DoWiD-wsn/avr-based_sensor_node/source/_asnx_lib_/i2c/i2c.c

/*!
 * @brief   ASN(x) I2C (TWI) library -- source file
 *
 * Library to support the use of the I2C module.
 *
 * @file    /_asnx_lib_/i2c/i2c.c
 * @author  Dominik Widhalm
 * @version 1.2.1
 * @date    2021/12/29
 */


/***** INCLUDES *******************************************************/
#include "i2c.h"


/***** FUNCTIONS ******************************************************/
/*!
 * Initialize the I2C interface as master.
 */
void i2c_init(void) {
    /* Initialize TWI clock with no prescaler */
    TWSR = 0;
    /* TWBR should be >10 for stable operation */
    TWBR = (uint8_t)(((F_CPU/I2C_SCL_CLK)-16.0)/2.0);
}


/*!
 * Reset the I2C interface (necessary after sleep).
 */
void i2c_reset(void) {
    /* Disable TWI */
    TWCR &= ~((1 << TWSTO) | (1 << TWEN));
    /* Re-enable TWI */
    TWCR |= (1 << TWEN);
}


/*!
 * Check if a device is available at the given address.
 *
 * @param[in]   addr        The device I2C address
 * @return      OK if device is available; ERROR otherwise
 */
I2C_RET_t i2c_is_available(uint8_t addr) {
    return i2c_write_raw(addr, 0x00);
}


/*!
 * Stop I2C data transfer and release I2C bus.
 *
 * @return      OK in case of success; ERROR otherwise
 */
I2C_RET_t i2c_stop(void) {
    /* Timeout counter */
    uint8_t timeout = 0;
    /* Send STOP condition */
    TWCR = _BV(TWINT) | _BV(TWEN) | _BV(TWSTO);
    /* Wait until STOP condition is executed and bus released */
    timeout = 0;
    while(TWCR & _BV(TWSTO)){
        /* Check if timeout has been reached */
        if(timeout++ >= I2C_WAIT_TIMEOUT) {
            /* Something's wrong ... */
            return I2C_RET_ERROR;
        }
    }
    /* Return success */
    return I2C_RET_OK;
}


/*!
 * Send I2C start condition, address and transfer direction.
 *
 * @param[in]   addr        Address of I2C device
 * @param[in]   dir         Transfer direction (R/W)
 * @return      OK in case of success; ERROR otherwise
 */
I2C_RET_t i2c_start(uint8_t addr, I2C_DIR_t dir) {
    /* Variable to temporary store status register value */
    uint8_t status_tmp;
    /* Timeout counter */
    uint8_t timeout = 0;
    /* Send START condition */
    TWCR = _BV(TWINT) | _BV(TWSTA) | _BV(TWEN);
    /* Wait until transmission completed */
    timeout = 0;
    while(!(TWCR & _BV(TWINT))) {
        /* Check if timeout has been reached */
        if(timeout++ >= I2C_WAIT_TIMEOUT) {
            /* Something's wrong ... */
            return I2C_RET_ERROR;
        }
    }
    /* Check value of TWI status register */
    status_tmp = TW_STATUS;
    if((status_tmp != TW_START) && (status_tmp != TW_REP_START)) {
        /* Something's wrong ... */
        return I2C_RET_ERROR;
    }

    /* Send device address */
    TWDR = (addr<<1) | dir;
    TWCR = _BV(TWINT) | _BV(TWEN);
    /* Wail until transmission completed and ACK/NACK has been received */
    timeout = 0;
    while(!(TWCR & _BV(TWINT))) {
        /* Check if timeout has been reached */
        if(timeout++ >= I2C_WAIT_TIMEOUT) {
            /* Something's wrong ... */
            return I2C_RET_ERROR;
        }
    }
    /* Check value of TWI status register */
    status_tmp = TW_STATUS;
    if((status_tmp != TW_MT_SLA_ACK) && (status_tmp != TW_MR_SLA_ACK)) {
        /* Something's wrong ... */
        return I2C_RET_ERROR;
    }
    /* Return success */
    return I2C_RET_OK;
}


/*!
 * Send I2C repeated start condition, address and transfer direction.
 * If device is busy, use ack polling to wait until device ready.
 *
 * @param[in]   addr        Address of I2C device
 * @param[in]   dir         Transfer direction (R/W)
 * @return      OK in case of success; ERROR otherwise
 */
I2C_RET_t i2c_start_wait(uint8_t addr, I2C_DIR_t dir) {
    /* Variable to temporary store status register value */
    uint8_t status_tmp;
    /* Try counter */
    uint8_t try = 0;
    /* Timeout counter */
    uint8_t timeout = 0;
    /* Try until success or timeout reached */
    while(1) {
        /* Check if timeout has been reached */
        if(try++ >= I2C_WAIT_TIMEOUT) {
            /* Something's wrong ... */
            return I2C_RET_ERROR;
        }
        /* Send START condition */
        TWCR = _BV(TWINT) | _BV(TWSTA) | _BV(TWEN);
        /* Wait until transmission completed */
        timeout = 0;
        while(!(TWCR & _BV(TWINT))) {
            /* Check if timeout has been reached */
            if(timeout++ >= I2C_WAIT_TIMEOUT) {
                /* Something's wrong ... */
                return I2C_RET_ERROR;
            }
        }
        /* Check value of TWI status register */
        status_tmp = TW_STATUS;
        if((status_tmp != TW_START) && (status_tmp != TW_REP_START)) {
            /* Give it another try ... */
            continue;
        }
        /* Send device address */
        TWDR = (addr<<1) | dir;
        TWCR = _BV(TWINT) | _BV(TWEN);
        /* Wail until transmission completed */
        timeout = 0;
        while(!(TWCR & _BV(TWINT))) {
            /* Check if timeout has been reached */
            if(timeout++ >= I2C_WAIT_TIMEOUT) {
                /* Something's wrong ... */
                return I2C_RET_ERROR;
            }
        }
        /* Check value of TWI status register */
        status_tmp = TW_STATUS;
        if((status_tmp == TW_MT_SLA_NACK) || (status_tmp ==TW_MR_DATA_NACK)) {
            /* Device busy, send stop condition to terminate write operation */
            i2c_stop();
            /* Give it another try ... */
            continue;
        }
        /* Looks like we've gone through ... */
        break;
    }
    /* Return success */
    return I2C_RET_OK;
}


/*!
 * Write one byte to I2C device.
 *
 * @param[in]   data        Data byte to be transferred
 * @return      OK in case of success; ERROR otherwise
 */
I2C_RET_t i2c_put(uint8_t data) {
    /* Timeout counter */
    uint8_t timeout = 0;
    /* Variable to temporary store status register value */
    uint8_t status_tmp;
    /* Send data to the previously addressed device */
    TWDR = data;
    TWCR = _BV(TWINT) | _BV(TWEN);
    /* Wait until transmission completed */
    timeout = 0;
    while(!(TWCR & _BV(TWINT))) {
        /* Check if timeout has been reached */
        if(timeout++ >= I2C_WAIT_TIMEOUT) {
            /* Something's wrong ... */
            return I2C_RET_ERROR;
        }
    }
    /* Check value of TWI status register */
    status_tmp = TW_STATUS;
    if(status_tmp != TW_MT_DATA_ACK) {
        /* Something's wrong ... */
        return I2C_RET_ERROR;
    }
    /* Return success */
    return I2C_RET_OK;
}


/*!
 * Read one byte from the I2C device with ACK (request more data from device).
 *
 * @param[out]  data        Data byte memory location
 * @return      OK in case of success; ERROR otherwise
 */
I2C_RET_t i2c_get_ack(uint8_t* data) {
    /* Timeout counter */
    uint8_t timeout = 0;
    /* Send a read request with acknowledgement (ack) */
    TWCR = _BV(TWINT) | _BV(TWEN) | _BV(TWEA);
    /* Wait until read is complete */
    timeout = 0;
    while(!(TWCR & _BV(TWINT))) {
        /* Check if timeout has been reached */
        if(timeout++ >= I2C_WAIT_TIMEOUT) {
            /* Something's wrong ... */
            return I2C_RET_ERROR;
        }
    }
    /* Copy the received byte */
    *data = TWDR;
    /* Return success */
    return I2C_RET_OK;
}


/*!
 * Read one byte from the I2C device with NACK (read is followed by a stop condition).
 *
 * @param[out]  data        Data byte memory location
 * @return      OK in case of success; ERROR otherwise
 */
I2C_RET_t i2c_get_nack(uint8_t* data) {
    /* Timeout counter */
    uint8_t timeout = 0;
    /* Send a read request without acknowledgement (nack) */
    TWCR = _BV(TWINT) | _BV(TWEN);
    /* Wait until read is complete */
    timeout = 0;
    while(!(TWCR & _BV(TWINT))) {
        /* Check if timeout has been reached */
        if(timeout++ >= I2C_WAIT_TIMEOUT) {
            /* Something's wrong ... */
            return I2C_RET_ERROR;
        }
    }
    /* Copy the received byte */
    *data = TWDR;
    /* Return success */
    return I2C_RET_OK;
}


/*!
 * Write 8-bit data to a given I2C address.
 *
 * @param[in]   addr        Address of I2C device
 * @param[in]   value       Data byte to be written
 * @return      OK in case of success; ERROR otherwise
 */
I2C_RET_t i2c_write_raw(uint8_t addr, uint8_t value) {
    /* Start in writing mode */
    if(i2c_start_wait(addr, I2C_WRITE) != I2C_RET_OK) {
        /* Start failed */
        return I2C_RET_ERROR;
    }
    /* Write value byte */
    if(i2c_put(value) != I2C_RET_OK) {
        /* Write byte failed */
        return I2C_RET_ERROR;
    }
    /* Stop writing mode */
    if(i2c_stop() != I2C_RET_OK) {
        /* Stop failed */
        return I2C_RET_ERROR;
    }
    /* Return with success */
    return I2C_RET_OK;
}


/*!
 * Read 8-bit data from a given I2C address.
 *
 * @param[in]   addr        Address of I2C device
 * @param[out]  value       Data byte memory location
 * @return      OK in case of success; ERROR otherwise
 */
I2C_RET_t i2c_read_raw(uint8_t addr, uint8_t* value) {
    /* Start in reading mode */
    if(i2c_start_wait(addr, I2C_READ) != I2C_RET_OK) {
        /* Start failed */
        return I2C_RET_ERROR;
    }
    /* Read a byte */
    uint8_t tmp;
    /* Read with NACK */
    if(i2c_get_nack(&tmp) == I2C_RET_OK) {
        /* Copy read byte */
        *value = tmp;
    } else {
        /* Read failed */
        return I2C_RET_ERROR;
    }
    /* Stop reading mode */
    if(i2c_stop() != I2C_RET_OK) {
        /* Stop failed */
        return I2C_RET_ERROR;
    }
    /* Return with success */
    return I2C_RET_OK;
}


/*!
 * Write a defined number of data bytes to a register of a given I2C address.
 *
 * @param[in]   addr        Address of I2C device
 * @param[in]   reg         Device register address
 * @param[in]   value       Data bytes to be written
 * @param[in]   len         Number of bytes to be written
 * @return      OK in case of success; ERROR otherwise
 */
I2C_RET_t i2c_write_block(uint8_t addr, uint8_t reg, uint8_t* value, uint8_t len) {
    /* Start in writing mode */
    if(i2c_start_wait(addr, I2C_WRITE) != I2C_RET_OK) {
        /* Start failed */
        return I2C_RET_ERROR;
    }
    /* Write register address */
    if(i2c_put(reg) != I2C_RET_OK) {
        /* Write address failed */
        return I2C_RET_ERROR;
    }
    /* Write "len" bytes */
    uint8_t cnt;
    for(cnt=0; cnt<len; cnt++) {
        /* Write cnt. byte */
        if(i2c_put(value[cnt]) != I2C_RET_OK) {
            /* Write byte failed */
            return I2C_RET_ERROR;
        }
    }
    /* Stop writing mode */
    if(i2c_stop() != I2C_RET_OK) {
        /* Stop failed */
        return I2C_RET_ERROR;
    }
    /* Return with success */
    return I2C_RET_OK;
}


/*!
 * Write 8-bit data to a register of a given I2C address.
 *
 * @param[in]   addr        Address of I2C device
 * @param[in]   reg         Device register address
 * @param[in]   value       8-bit data to be written
 * @return      OK in case of success; ERROR otherwise
 */
I2C_RET_t i2c_write_8(uint8_t addr, uint8_t reg, uint8_t value) {
    /* Start in writing mode */
    if(i2c_start_wait(addr, I2C_WRITE) != I2C_RET_OK) {
        /* Start failed */
        return I2C_RET_ERROR;
    }
    /* Write register address */
    if(i2c_put(reg) != I2C_RET_OK) {
        /* Write address failed */
        return I2C_RET_ERROR;
    }
    /* Write value byte */
    if(i2c_put(value) != I2C_RET_OK) {
        /* Write byte failed */
        return I2C_RET_ERROR;
    }
    /* Stop writing mode */
    if(i2c_stop() != I2C_RET_OK) {
        /* Stop failed */
        return I2C_RET_ERROR;
    }
    /* Return with success */
    return I2C_RET_OK;
}


/*!
 * Write 16-bit data to a register of a given I2C address.
 *
 * @param[in]   addr        Address of I2C device
 * @param[in]   reg         Device register address
 * @param[in]   value       16-bit data to be written
 * @return      OK in case of success; ERROR otherwise
 */
I2C_RET_t i2c_write_16(uint8_t addr, uint8_t reg, uint16_t value) {
    /* Start in writing mode */
    if(i2c_start_wait(addr, I2C_WRITE) != I2C_RET_OK) {
        /* Start failed */
        return I2C_RET_ERROR;
    }
    /* Write register address */
    if(i2c_put(reg) != I2C_RET_OK) {
        /* Write address failed */
        return I2C_RET_ERROR;
    }
    /* Write value lower byte */
    if(i2c_put(value & 0x00FF) != I2C_RET_OK) {
        /* Write byte failed */
        return I2C_RET_ERROR;
    }
    /* Write value higher byte */
    if(i2c_put((value & 0xFF00) >> 8) != I2C_RET_OK) {
        /* Write byte failed */
        return I2C_RET_ERROR;
    }
    /* Stop writing mode */
    if(i2c_stop() != I2C_RET_OK) {
        /* Stop failed */
        return I2C_RET_ERROR;
    }
    /* Return with success */
    return I2C_RET_OK;
}


/*!
 * Read a defined number of data bytes from a register of a given I2C address.
 *
 * @param[in]   addr        Address of I2C device
 * @param[in]   reg         Device register address
 * @param[out]  value       Data bytes memory location
 * @param[in]   len         Number of bytes to be read
 * @return      OK in case of success; ERROR otherwise
 */
I2C_RET_t i2c_read_block(uint8_t addr, uint8_t reg, uint8_t* value, uint8_t len) {
    /* Start in writing mode */
    if(i2c_start_wait(addr, I2C_WRITE) != I2C_RET_OK) {
        /* Start failed */
        return I2C_RET_ERROR;
    }
    /* Write register address */
    if(i2c_put(reg) != I2C_RET_OK) {
        /* Write address failed */
        return I2C_RET_ERROR;
    }
    /* Stop writing mode */
    if(i2c_stop() != I2C_RET_OK) {
        /* Write byte failed */
        return I2C_RET_ERROR;
    }
    
    /* Restart in reading mode */
    if(i2c_start_wait(addr, I2C_READ) != I2C_RET_OK) {
        /* Start failed */
        return I2C_RET_ERROR;
    }
    /* Read "len" bytes */
    uint8_t cnt,tmp;
    for(cnt=0; cnt<len; cnt++) {
        /* Check whether it is the last byte to read */
        if(cnt<(len-1)) {
            /* Read with ACK */
            if(i2c_get_ack(&tmp) == I2C_RET_OK) {
                /* Copy read byte */
                value[cnt] = tmp;
            } else {
                /* Read failed */
                return I2C_RET_ERROR;
            }
        } else {
            /* Read with NACK */
            if(i2c_get_nack(&tmp) == I2C_RET_OK) {
                /* Copy read byte */
                value[cnt] = tmp;
            } else {
                /* Read failed */
                return I2C_RET_ERROR;
            }
        }
    }
    /* Stop reading mode */
    if(i2c_stop() != I2C_RET_OK) {
        /* Stop failed */
        return I2C_RET_ERROR;
    }
    /* Return with success */
    return I2C_RET_OK;
}


/*!
 * Read 8-bit data (unsigned) from a register of a given I2C address.
 *
 * @param[in]   addr        Address of I2C device
 * @param[in]   reg         Device register address
 * @param[out]  value       8-bit data memory location
 * @return      OK in case of success; ERROR otherwise
 */
I2C_RET_t i2c_read_U8(uint8_t addr, uint8_t reg, uint8_t* value) {
/* Start in writing mode */
    if(i2c_start_wait(addr, I2C_WRITE) != I2C_RET_OK) {
        /* Start failed */
        return I2C_RET_ERROR;
    }
    /* Write register address */
    if(i2c_put(reg) != I2C_RET_OK) {
        /* Write address failed */
        return I2C_RET_ERROR;
    }
    /* Stop writing mode */
    if(i2c_stop() != I2C_RET_OK) {
        /* Write byte failed */
        return I2C_RET_ERROR;
    }
    
    /* Restart in reading mode */
    if(i2c_start_wait(addr, I2C_READ) != I2C_RET_OK) {
        /* Start failed */
        return I2C_RET_ERROR;
    }
    /* Read 8 bit */
    uint8_t tmp;
    /* Read with NACK */
    if(i2c_get_nack(&tmp) == I2C_RET_OK) {
        /* Copy read byte */
        *value = tmp;
    } else {
        /* Read failed */
        return I2C_RET_ERROR;
    }
    /* Stop reading mode */
    if(i2c_stop() != I2C_RET_OK) {
        /* Stop failed */
        return I2C_RET_ERROR;
    }
    /* Return with success */
    return I2C_RET_OK;
}


/*!
 * Read signed 8-bit data from a register of a given I2C address.
 *
 * @param[in]   addr        Address of I2C device
 * @param[in]   reg         Device register address
 * @param[out]  value       Signed 8-bit data memory location
 * @return      OK in case of success; ERROR otherwise
 */
I2C_RET_t i2c_read_S8(uint8_t addr, uint8_t reg, int8_t* value) {
    uint8_t tmp;
    /* Read 8-bit unsigned */
    if(i2c_read_U8(addr, reg, &tmp) != I2C_RET_OK) {
        /* Read failed */
        return I2C_RET_ERROR;
    }
    /* Check if tmp sign bit is set */
    if(tmp > 127) {
        /* Negative value */
        *value = tmp-256;
    } else {
        /* Positive value */
        *value = tmp;
    }
    /* Return with success */
    return I2C_RET_OK;
}


/*!
 * Read 16-bit data (unsigned) with a given endianess from a register of a given I2C address.
 *
 * @param[in]   addr        Address of I2C device
 * @param[in]   reg         Device register address
 * @param[out]  value       16-bit data memory location
 * @param[in]   endian      Endianess of the data bytes
 * @return      OK in case of success; ERROR otherwise
 */
I2C_RET_t i2c_read_U16(uint8_t addr, uint8_t reg, uint16_t* value, I2C_ENDIAN_t endian) {
    uint8_t tmp[2];
    /* Read two byte */
    if(i2c_read_block(addr, reg, tmp, 2) != I2C_RET_OK) {
        /* Read failed */
        return I2C_RET_ERROR;
    }
    /* Swap bytes if using big endian */
    if(endian == I2C_ENDIAN_BIG) {
        /* Big Endian */
        *value = ((uint16_t)tmp[0]<<8) | (uint16_t)tmp[1];
    } else {
        /* Little Endian */
        *value = ((uint16_t)tmp[1]<<8) | (uint16_t)tmp[0];
    }
    /* Return with success */
    return I2C_RET_OK;
}


/*!
 * Read signed 16-bit data with a given endianess from a register of a given I2C address.
 *
 * @param[in]   addr        Address of I2C device
 * @param[in]   reg         Device register address
 * @param[out]  value       Signed 16-bit data memory location
 * @param[in]   endian      Endianess of the data bytes
 * @return      OK in case of success; ERROR otherwise
 */
I2C_RET_t i2c_read_S16(uint8_t addr, uint8_t reg, int16_t* value, I2C_ENDIAN_t endian) {
    uint16_t tmp;
    /* Read 16-bit unsigned */
    if(i2c_read_U16(addr, reg, &tmp, endian) != I2C_RET_OK) {
        /* Read failed */
        return I2C_RET_ERROR;
    }
    /* Check if tmp sign bit is set */
    if(tmp > 32767) {
        /* Negative value */
        *value = tmp-65536;
    } else {
        /* Positive value */
        *value = tmp;
    }
    /* Return with success */
    return I2C_RET_OK;
}


/*!
 * Read 16-bit little endian data (unsigned) from a register of a given I2C address.
 *
 * @param[in]   addr        Address of I2C device
 * @param[in]   reg         Device register address
 * @param[out]  value       16-bit LE data memory location
 * @return      OK in case of success; ERROR otherwise
 */
I2C_RET_t i2c_read_U16LE(uint8_t addr, uint8_t reg, uint16_t* value) {
    uint16_t tmp;
    /* Read 16-bit unsigned */
    if(i2c_read_U16(addr, reg, &tmp, I2C_ENDIAN_LITTLE) != I2C_RET_OK) {
        /* Read failed */
        return I2C_RET_ERROR;
    }
    /* Copy value */
    *value = tmp;
    /* Return with success */
    return I2C_RET_OK;
}


/*!
 * Read 16-bit big endian data (unsigned) from a register of a given I2C address.
 *
 * @param[in]   addr        Address of I2C device
 * @param[in]   reg         Device register address
 * @param[out]  value       16-bit BE data memory location
 * @return      OK in case of success; ERROR otherwise
 */
I2C_RET_t i2c_read_U16BE(uint8_t addr, uint8_t reg, uint16_t* value) {
    uint16_t tmp;
    /* Read 16-bit unsigned */
    if(i2c_read_U16(addr, reg, &tmp, I2C_ENDIAN_BIG) != I2C_RET_OK) {
        /* Read failed */
        return I2C_RET_ERROR;
    }
    /* Copy value */
    *value = tmp;
    /* Return with success */
    return I2C_RET_OK;
}


/*!
 * Read signed 16-bit little endian data from a register of a given I2C address.
 *
 * @param[in]   addr        Address of I2C device
 * @param[in]   reg         Device register address
 * @param[out]  value       Signed 16-bit LE data memory location
 * @return      OK in case of success; ERROR otherwise
 */
I2C_RET_t i2c_read_S16LE(uint8_t addr, uint8_t reg, int16_t* value) {
    int16_t tmp;
    /* Read 16-bit signed */
    if(i2c_read_S16(addr, reg, &tmp, I2C_ENDIAN_LITTLE) != I2C_RET_OK) {
        /* Read failed */
        return I2C_RET_ERROR;
    }
    /* Copy value */
    *value = tmp;
    /* Return with success */
    return I2C_RET_OK;
}


/*!
 * Read signed 16-bit big endian data from a register of a given I2C address.
 *
 * @param[in]   addr        Address of I2C device
 * @param[in]   reg         Device register address
 * @param[out]  value       Signed 16-bit BE data memory location
 * @return      OK in case of success; ERROR otherwise
 */
I2C_RET_t i2c_read_S16BE(uint8_t addr, uint8_t reg, int16_t* value) {
    int16_t tmp;
    /* Read 16-bit signed */
    if(i2c_read_S16(addr, reg, &tmp, I2C_ENDIAN_BIG) != I2C_RET_OK) {
        /* Read failed */
        return I2C_RET_ERROR;
    }
    /* Copy value */
    *value = tmp;
    /* Return with success */
    return I2C_RET_OK;
}


/*!
 * Write a defined number of data bytes to a 16-bit register address of a given I2C address.
 *
 * @param[in]   addr        Address of I2C device
 * @param[in]   reg         16-bit device register address
 * @param[in]   value       Data bytes to be written
 * @param[in]   len         Number of bytes to be written
 * @return      OK in case of success; ERROR otherwise
 */
I2C_RET_t i2c_write16_block(uint8_t addr, uint16_t reg, uint8_t* value, uint8_t len) {
    /* Start in writing mode */
    if(i2c_start_wait(addr, I2C_WRITE) != I2C_RET_OK) {
        /* Start failed */
        return I2C_RET_ERROR;
    }
    /* Write register address low byte */
    if(i2c_put(reg & 0x00FF) != I2C_RET_OK) {
        /* Write address failed */
        return I2C_RET_ERROR;
    }
    /* Write register address high byte */
    if(i2c_put((reg & 0xFF00)>>8) != I2C_RET_OK) {
        /* Write address failed */
        return I2C_RET_ERROR;
    }
    /* Write "len" bytes */
    uint8_t cnt;
    for(cnt=0; cnt<len; cnt++) {
        /* Write cnt. byte */
        if(i2c_put(value[cnt]) != I2C_RET_OK) {
            /* Write byte failed */
            return I2C_RET_ERROR;
        }
    }
    /* Stop writing mode */
    if(i2c_stop() != I2C_RET_OK) {
        /* Stop failed */
        return I2C_RET_ERROR;
    }
    /* Return with success */
    return I2C_RET_OK;
}


/*!
 * Write 8-bit data to a 16-bit register address of a given I2C address.
 *
 * @param[in]   addr        Address of I2C device
 * @param[in]   reg         16-bit device register address
 * @param[in]   value       8-bit data to be written
 * @return      OK in case of success; ERROR otherwise
 */
I2C_RET_t i2c_write16_8(uint8_t addr, uint16_t reg, uint8_t value) {
    /* Start in writing mode */
    if(i2c_start_wait(addr, I2C_WRITE) != I2C_RET_OK) {
        /* Start failed */
        return I2C_RET_ERROR;
    }
    /* Write register address low byte */
    if(i2c_put(reg & 0x00FF) != I2C_RET_OK) {
        /* Write address failed */
        return I2C_RET_ERROR;
    }
    /* Write register address high byte */
    if(i2c_put((reg & 0xFF00)>>8) != I2C_RET_OK) {
        /* Write address failed */
        return I2C_RET_ERROR;
    }
    /* Write value byte */
    if(i2c_put(value) != I2C_RET_OK) {
        /* Write byte failed */
        return I2C_RET_ERROR;
    }
    /* Stop writing mode */
    if(i2c_stop() != I2C_RET_OK) {
        /* Stop failed */
        return I2C_RET_ERROR;
    }
    /* Return with success */
    return I2C_RET_OK;
}


/*!
 * Write 16-bit data to a 16-bit register address of a given I2C address.
 *
 * @param[in]   addr        Address of I2C device
 * @param[in]   reg         16-bit device register address
 * @param[in]   value       16-bit data to be written
 * @return      OK in case of success; ERROR otherwise
 */
I2C_RET_t i2c_write16_16(uint8_t addr, uint16_t reg, uint16_t value) {
    /* Start in writing mode */
    if(i2c_start_wait(addr, I2C_WRITE) != I2C_RET_OK) {
        /* Start failed */
        return I2C_RET_ERROR;
    }
    /* Write register address low byte */
    if(i2c_put(reg & 0x00FF) != I2C_RET_OK) {
        /* Write address failed */
        return I2C_RET_ERROR;
    }
    /* Write register address high byte */
    if(i2c_put((reg & 0xFF00)>>8) != I2C_RET_OK) {
        /* Write address failed */
        return I2C_RET_ERROR;
    }
    /* Write value lower byte */
    if(i2c_put(value & 0x00FF) != I2C_RET_OK) {
        /* Write byte failed */
        return I2C_RET_ERROR;
    }
    /* Write value higher byte */
    if(i2c_put((value & 0xFF00) >> 8) != I2C_RET_OK) {
        /* Write byte failed */
        return I2C_RET_ERROR;
    }
    /* Stop writing mode */
    if(i2c_stop() != I2C_RET_OK) {
        /* Stop failed */
        return I2C_RET_ERROR;
    }
    /* Return with success */
    return I2C_RET_OK;
}


/*!
 * Read a defined number of data bytes from a 16-bit register address of a given I2C address.
 *
 * @param[in]   addr        Address of I2C device
 * @param[in]   reg         16-bit device register address
 * @param[out]  value       Data bytes memory location
 * @param[in]   len         Number of bytes to be read
 * @return      OK in case of success; ERROR otherwise
 */
I2C_RET_t i2c_read16_block(uint8_t addr, uint16_t reg, uint8_t* value, uint8_t len) {
    /* Start in writing mode */
    if(i2c_start_wait(addr, I2C_WRITE) != I2C_RET_OK) {
        /* Start failed */
        return I2C_RET_ERROR;
    }
    /* Write register address low byte */
    if(i2c_put(reg & 0x00FF) != I2C_RET_OK) {
        /* Write address failed */
        return I2C_RET_ERROR;
    }
    /* Write register address high byte */
    if(i2c_put((reg & 0xFF00)>>8) != I2C_RET_OK) {
        /* Write address failed */
        return I2C_RET_ERROR;
    }
    /* Stop writing mode */
    if(i2c_stop() != I2C_RET_OK) {
        /* Write byte failed */
        return I2C_RET_ERROR;
    }
    
    /* Restart in reading mode */
    if(i2c_start_wait(addr, I2C_READ) != I2C_RET_OK) {
        /* Start failed */
        return I2C_RET_ERROR;
    }
    /* Read "len" bytes */
    uint8_t cnt,tmp;
    for(cnt=0; cnt<len; cnt++) {
        /* Check whether it is the last byte to read */
        if(cnt<(len-1)) {
            /* Read with ACK */
            if(i2c_get_ack(&tmp) == I2C_RET_OK) {
                /* Copy read byte */
                value[cnt] = tmp;
            } else {
                /* Read failed */
                return I2C_RET_ERROR;
            }
        } else {
            /* Read with NACK */
            if(i2c_get_nack(&tmp) == I2C_RET_OK) {
                /* Copy read byte */
                value[cnt] = tmp;
            } else {
                /* Read failed */
                return I2C_RET_ERROR;
            }
        }
    }
    /* Stop reading mode */
    if(i2c_stop() != I2C_RET_OK) {
        /* Stop failed */
        return I2C_RET_ERROR;
    }
    /* Return with success */
    return I2C_RET_OK;
}


/*!
 * Read 8-bit data (unsigned) from a 16-bit register address of a given I2C address.
 *
 * @param[in]   addr        Address of I2C device
 * @param[in]   reg         16-bit device register address
 * @param[out]  value       8-bit data memory location
 * @return      OK in case of success; ERROR otherwise
 */
I2C_RET_t i2c_read16_U8(uint8_t addr, uint16_t reg, uint8_t* value) {
/* Start in writing mode */
    if(i2c_start_wait(addr, I2C_WRITE) != I2C_RET_OK) {
        /* Start failed */
        return I2C_RET_ERROR;
    }
    /* Write register address low byte */
    if(i2c_put(reg & 0x00FF) != I2C_RET_OK) {
        /* Write address failed */
        return I2C_RET_ERROR;
    }
    /* Write register address high byte */
    if(i2c_put((reg & 0xFF00)>>8) != I2C_RET_OK) {
        /* Write address failed */
        return I2C_RET_ERROR;
    }
    /* Stop writing mode */
    if(i2c_stop() != I2C_RET_OK) {
        /* Write byte failed */
        return I2C_RET_ERROR;
    }
    
    /* Restart in reading mode */
    if(i2c_start_wait(addr, I2C_READ) != I2C_RET_OK) {
        /* Start failed */
        return I2C_RET_ERROR;
    }
    /* Read 8 bit */
    uint8_t tmp;
    /* Read with NACK */
    if(i2c_get_nack(&tmp) == I2C_RET_OK) {
        /* Copy read byte */
        *value = tmp;
    } else {
        /* Read failed */
        return I2C_RET_ERROR;
    }
    /* Stop reading mode */
    if(i2c_stop() != I2C_RET_OK) {
        /* Stop failed */
        return I2C_RET_ERROR;
    }
    /* Return with success */
    return I2C_RET_OK;
}


/*!
 * Read signed 8-bit data from a 16-bit register address of a given I2C address.
 *
 * @param[in]   addr        Address of I2C device
 * @param[in]   reg         16-bit device register address
 * @param[out]  value       Signed 8-bit data memory location
 * @return      OK in case of success; ERROR otherwise
 */
I2C_RET_t i2c_read16_S8(uint8_t addr, uint16_t reg, int8_t* value) {
    uint8_t tmp;
    /* Read 8-bit unsigned */
    if(i2c_read16_U8(addr, reg, &tmp) != I2C_RET_OK) {
        /* Read failed */
        return I2C_RET_ERROR;
    }
    /* Check if tmp sign bit is set */
    if(tmp > 127) {
        /* Negative value */
        *value = tmp-256;
    } else {
        /* Positive value */
        *value = tmp;
    }
    /* Return with success */
    return I2C_RET_OK;
}


/*!
 * Read 16-bit data (unsigned) with a given endianess from a 16-bit register address of a given I2C address.
 *
 * @param[in]   addr        Address of I2C device
 * @param[in]   reg         16-bit device register address
 * @param[out]  value       16-bit data memory location
 * @param[in]   endian      Endianess of the data bytes
 * @return      OK in case of success; ERROR otherwise
 */
I2C_RET_t i2c_read16_U16(uint8_t addr, uint16_t reg, uint16_t* value, I2C_ENDIAN_t endian) {
    uint8_t tmp[2];
    /* Read two byte */
    if(i2c_read16_block(addr, reg, tmp, 2) != I2C_RET_OK) {
        /* Read failed */
        return I2C_RET_ERROR;
    }
    /* Swap bytes if using big endian */
    if(endian == I2C_ENDIAN_BIG) {
        /* Big Endian */
        *value = ((uint16_t)tmp[0]<<8) | (uint16_t)tmp[1];
    } else {
        /* Little Endian */
        *value = ((uint16_t)tmp[1]<<8) | (uint16_t)tmp[0];
    }
    /* Return with success */
    return I2C_RET_OK;
}


/*!
 * Read signed 16-bit data with a given endianess from a 16-bit register address of a given I2C address.
 *
 * @param[in]   addr        Address of I2C device
 * @param[in]   reg         16-bit device register address
 * @param[out]  value       Signed 16-bit data memory location
 * @param[in]   endian      Endianess of the data bytes
 * @return      OK in case of success; ERROR otherwise
 */
I2C_RET_t i2c_read16_S16(uint8_t addr, uint16_t reg, int16_t* value, I2C_ENDIAN_t endian) {
    uint16_t tmp;
    /* Read 16-bit unsigned */
    if(i2c_read16_U16(addr, reg, &tmp, endian) != I2C_RET_OK) {
        /* Read failed */
        return I2C_RET_ERROR;
    }
    /* Check if tmp sign bit is set */
    if(tmp > 32767) {
        /* Negative value */
        *value = tmp-65536;
    } else {
        /* Positive value */
        *value = tmp;
    }
    /* Return with success */
    return I2C_RET_OK;
}


/*!
 * Read 16-bit little endian data (unsigned) from a 16-bit register address of a given I2C address.
 *
 * @param[in]   addr        Address of I2C device
 * @param[in]   reg         16-bit device register address
 * @param[out]  value       16-bit LE data memory location
 * @return      OK in case of success; ERROR otherwise
 */
I2C_RET_t i2c_read16_U16LE(uint8_t addr, uint16_t reg, uint16_t* value) {
    uint16_t tmp;
    /* Read 16-bit unsigned */
    if(i2c_read16_U16(addr, reg, &tmp, I2C_ENDIAN_LITTLE) != I2C_RET_OK) {
        /* Read failed */
        return I2C_RET_ERROR;
    }
    /* Copy value */
    *value = tmp;
    /* Return with success */
    return I2C_RET_OK;
}


/*!
 * Read 16-bit big endian data (unsigned) from a 16-bit register address of a given I2C address.
 *
 * @param[in]   addr        Address of I2C device
 * @param[in]   reg         16-bit device register address
 * @param[out]  value       16-bit BE data memory location
 * @return      OK in case of success; ERROR otherwise
 */
I2C_RET_t i2c_read16_U16BE(uint8_t addr, uint16_t reg, uint16_t* value) {
    uint16_t tmp;
    /* Read 16-bit unsigned */
    if(i2c_read16_U16(addr, reg, &tmp, I2C_ENDIAN_BIG) != I2C_RET_OK) {
        /* Read failed */
        return I2C_RET_ERROR;
    }
    /* Copy value */
    *value = tmp;
    /* Return with success */
    return I2C_RET_OK;
}


/*!
 * Read signed 16-bit little endian data from a 16-bit register address of a given I2C address.
 *
 * @param[in]   addr        Address of I2C device
 * @param[in]   reg         16-bit device register address
 * @param[out]  value       Signed 16-bit LE data memory location
 * @return      OK in case of success; ERROR otherwise
 */
I2C_RET_t i2c_read16_S16LE(uint8_t addr, uint16_t reg, int16_t* value) {
    int16_t tmp;
    /* Read 16-bit signed */
    if(i2c_read16_S16(addr, reg, &tmp, I2C_ENDIAN_LITTLE) != I2C_RET_OK) {
        /* Read failed */
        return I2C_RET_ERROR;
    }
    /* Copy value */
    *value = tmp;
    /* Return with success */
    return I2C_RET_OK;
}


/*!
 * Read signed 16-bit big endian data from a 16-bit register address of a given I2C address.
 *
 * @param[in]   addr        Address of I2C device
 * @param[in]   reg         16-bit device register address
 * @param[out]  value       Signed 16-bit BE data memory location
 * @return      OK in case of success; ERROR otherwise
 */
I2C_RET_t i2c_read16_S16BE(uint8_t addr, uint16_t reg, int16_t* value) {
    int16_t tmp;
    /* Read 16-bit signed */
    if(i2c_read16_S16(addr, reg, &tmp, I2C_ENDIAN_BIG) != I2C_RET_OK) {
        /* Read failed */
        return I2C_RET_ERROR;
    }
    /* Copy value */
    *value = tmp;
    /* Return with success */
    return I2C_RET_OK;
}
