DoWiD-wsn/avr-based_sensor_node/source/_asnx_lib_/sensors/stemma_soil.c

/*!
 * @brief   ASN(x) STEMMA SOIL sensor library -- source file
 *
 * Library to support the STEMMA SOIL sensor.
 *
 * @file    /_asnx_lib_/sensors/stemma_soil.c
 * @author  Dominik Widhalm
 * @version 1.2.0
 * @date    2021/06/07
 *
 * @see     https://learn.adafruit.com/adafruit-stemma-soil-sensor-i2c-capacitive-moisture-sensor/
 * @see     https://github.com/adafruit/Adafruit_Seesaw
 */


/***** INCLUDES *******************************************************/
#include "stemma_soil.h"


/***** FUNCTIONS ******************************************************/
/*!
 * Initialization of the STEMMA SOIL sensor.
 *
 * @param[out]  dev             Device structure to be filled
 * @param[in]   address         I2C address of the sensor
 */
STEMMA_RET_t stemma_init(STEMMA_t* dev, uint8_t address) {
   /* Check if the device is available */
   if(i2c_is_available(address) == I2C_RET_OK) {
        /* Device is available ... store address in device structure */
        dev->address = address;
        /* Return OK */
        return STEMMA_RET_OK;
   } else {
        /* Return ERROR */
        return STEMMA_RET_ERROR_NODEV;
   }
}


/*!
 * Read the version code of the STEMMA SOIL sensor.
 * Bits [31:16] will be a date code, [15:0] will be the product id.
 * 
 * @param[in]   dev             Device structure
 * @param[out]  version         Version code read from the sensor
 * @return      OK in case of success; ERROR otherwise
 */
STEMMA_RET_t stemma_get_version(STEMMA_t* dev, uint32_t* version) {
    /* Variable for the read result */
    uint8_t res[4] = {0};
    /* Read in 4 bytes */
    if(i2c_read16_block(dev->address, (STEMMA_STATUS_BASE | (STEMMA_STATUS_VERSION<<8)), res, 4) != I2C_RET_OK) {
        /* Reading failed */
        return STEMMA_RET_ERROR;
    }
    /* Copy the result */
    *version = ((uint32_t)res[0] << 24) | ((uint32_t)res[1] << 16) | ((uint32_t)res[2] << 8) | (uint32_t)res[3];
    /* Return success */
    return STEMMA_RET_OK;
}


/*!
 * Read the temperature of the sensor in degrees Celsius (°C).
 * 
 * @param[in]   dev             Device structure
 * @param[out]  temperature     Sensor temperature in degrees Celsius (°C)
 * @return      OK in case of success; ERROR otherwise
 */
STEMMA_RET_t stemma_get_temperature(STEMMA_t* dev, float* temperature) {
    /* Variable for the read result */
    uint8_t res[4] = {0};
    /* Read in 4 bytes */
    if(i2c_read16_block(dev->address, (STEMMA_STATUS_BASE | (STEMMA_STATUS_TEMP<<8)), res, 4) != I2C_RET_OK) {
        /* Reading failed */
        return STEMMA_RET_ERROR;
    }
    /* Get intermediate result */
    uint32_t ret = ((uint32_t)res[0] << 24) | ((uint32_t)res[1] << 16) | ((uint32_t)res[2] << 8) | (uint32_t)res[3];
    /* Copy the result */
    *temperature = (1.0 / (1UL << 16)) * (float)ret;
    /* Return success */
    return STEMMA_RET_OK;
}


/*!
 * Read the humidity of the sensor indicated by its capacitance.
 * 
 * @param[in]   dev             Device structure
 * @param[out]  humidity        Humidity in percent
 * @return      OK in case of success; ERROR otherwise
 */
STEMMA_RET_t stemma_get_humidity(STEMMA_t* dev, float* humidity) {
    /* Variable for the read result */
    uint16_t ret = STEMMA_TOUCH_WORKING;
    /* Capacitance measurement can take some time */
    do {
        /* Read in 2 bytes */
        if(i2c_read16_U16BE(dev->address, (STEMMA_TOUCH_BASE | (STEMMA_TOUCH_CH0<<8)), &ret) != I2C_RET_OK) {
            /* Reading failed */
            return STEMMA_RET_ERROR;
        }
    }while(ret == STEMMA_TOUCH_WORKING);
    /* Copy the result */
    *humidity = (((float)ret - STEMMA_CAP_MIN) / (STEMMA_CAP_MAX - STEMMA_CAP_MIN)) * 100.0;
    /* Return success */
    return STEMMA_RET_OK;
}


/*!
 * Read the humidity of the sensor indicated by its capacitance and use
 * a floating average over a defined number of readings to smooth the value.
 * 
 * @param[in]   dev             Device structure
 * @param[in]   structure       Floating average structure
 * @param[out]  humidity        Humidity in percent
 * @return      OK in case of success; ERROR otherwise
 */
STEMMA_RET_t stemma_get_humidity_avg(STEMMA_t* dev, STEMMA_AVG_t* structure, float* humidity) {
    /* Temporary variable for the sensor reading */
    float tmp;
    /* Temporary counter variable */
    uint8_t i = 0;
    /* Static variable for the value array index */
    static uint8_t index = 0;
    /* Get a new reading */
    STEMMA_RET_t ret = stemma_get_humidity(dev, &tmp);
    /* Check if the reading is valid */
    if(ret != STEMMA_RET_OK) {
        /* Something went wrong */
        return ret;
    }
    /* Check if it is the first reading */
    if(structure->empty == 0) {
        for(i=0; i<STEMMA_AVG_CNT; i++) {
            structure->value[i] = tmp;
            index = 1;
        }
    } else {
        /* There are other readings available already */
        structure->value[index] = tmp;
        /* Get new index */
        index = (index+1) % STEMMA_AVG_CNT;
    }
    /* Calculate average */
    double sum = 0;
    for(i=0; i<STEMMA_AVG_CNT; i++) {
        sum += structure->value[i];
    }
    sum /= STEMMA_AVG_CNT;
    /* Copy result to pointer location */
    *humidity = sum;
    /* Return with success */
    return STEMMA_RET_OK;
}
