DoWiD-wsn/avr-based_sensor_node/source/_asnx_lib_/hw/led.h

/*!
 * @brief   ASN(x) user LED library -- header file
 *
 * Library to support the use of the ASN(x) user LEDs.
 *
 * @file    /_asnx_lib_/hw/led.h
 * @author  Dominik Widhalm
 * @version 1.2.0
 * @date    2021/06/07
 */

#ifndef _ASNX_LED_H_
#define _ASNX_LED_H_

/***** INCLUDES *******************************************************/
/*** STD ***/
#include <stdint.h>
#include <stddef.h>
/*** ASNX LIB ***/
#include "hw/hw.h"


/***** DEFINES ********************************************************/
/*! User LEDs DDR register */
#define LED_DDR                             DDRD
/*! User LEDs PORT register */
#define LED_PORT                            PORTD
/*! User LEDs PIN register */
#define LED_PIN                             PIND
/*! User LED1 portpin index */
#define LED1_GPIO                           PD5
/*! User LED2 portpin index */
#define LED2_GPIO                           PD4


/***** FUNCTION PROTOTYPES ********************************************/
void led_init(void);
void led1_low(void);
void led2_low(void);
void led1_high(void);
void led2_high(void);
void led1_toggle(void);
void led2_toggle(void);


#endif // _ASNX_LED_H_
