DoWiD-wsn/avr-based_sensor_node/source/005-xbee_sleep_demo/xbee_sleep_demo.c

/****
 * @brief   Demo application for the Xbee pin-sleep functionality.
 *
 * Demo application based on the sensor node demo (004), but with
 * Xbee pin-sleep enabled, that is, the xbee radio is only active
 * while updating the values and is put to sleep the remaining time.
 *
 * @file    /005-xbee_sleep_demo/xbee_sleep_demo.c
 * @author  $Author: Dominik Widhalm $
 * @version $Revision: 1.0 $
 * @date    $Date: 2021/05/05 $
 *****/


/*** DEMO CONFIGURATION ***/
/* Enable debug output via UART1 */
#define ENABLE_DBG              (1)

/* Update interval [min] */
#define UPDATE_INTERVAL         (10)

/* MAC address of the destination */
#define XBEE_DESTINATION_MAC    SEN_MSG_MAC_CH

/* Incident counter total threshold */
#define INCIDENT_TOTAL_MAX      (100)
/* Incident counter single threshold */
#define INCIDENT_SINGLE_MAX     (10)

/* Sensor node configuration (0 ... stemma soil, ds18b20 / 1 ... am2302) */
#define NODE_CONFIGURATION      (0)
/* Thermistor surface measurement available (0 ... no / 1 ... yes) */
#define NODE_103JT_AVAILABLE    (1)

/* Measurement message data indices */
#define MSG_VALUE_ADC_SELF      (0)
#define MSG_VALUE_MCU_VSS       (1)
#define MSG_VALUE_BAT_VSS       (2)
#define MSG_VALUE_XBEE_T        (3)
#define MSG_VALUE_XBEE_VSS      (4)
#define MSG_VALUE_103JT_T       (5)
#define MSG_VALUE_TMP275_T      (6)
#define MSG_VALUE_DS18B20_T     (7)
#define MSG_VALUE_STEMMA_H      (8)
#define MSG_VALUE_AM2302_T      (9)
#define MSG_VALUE_AM2302_H      (10)
#define MSG_VALUE_INCIDENT      (11)
#define MSG_VALUE_REBOOOT       (12)

/* Xbee sleep-request pin */
#define XBEE_SLEEP_REQ_DDR      (DDRC)
#define XBEE_SLEEP_REQ_PORT     (PORTC)
#define XBEE_SLEEP_REQ_PIN      (PINC)
#define XBEE_SLEEP_REQ_GPIO     (PC6)
/* Xbee sleep-indicator pin */
#define XBEE_SLEEP_IND_DDR      (DDRC)
#define XBEE_SLEEP_IND_PORT     (PORTC)
#define XBEE_SLEEP_IND_PIN      (PINC)
#define XBEE_SLEEP_IND_GPIO     (PC7)


/***** INCLUDES *******************************************************/
/*** AVR ***/
#include <avr/io.h>
#include <avr/interrupt.h>
#include <avr/wdt.h>
#include <util/delay.h>
/*** ASNX LIB ***/
/* MCU */
#include "adc/adc.h"
#include "hw/led.h"
#include "timer/systick.h"
#include "uart/uart.h"
/* Radio */
#include "xbee/xbee.h"
/* Sensors */
#include "sensors/tmp275.h"
TMP275_t tmp275;
#if NODE_CONFIGURATION==0
#  include "sensors/ds18x20.h"
DS18X20_t ds18b20;
#  include "sensors/stemma_soil.h"
STEMMA_t stemma;
#elif NODE_CONFIGURATION==1
#  include "sensors/dht.h"
DHT_t am2302;
#endif
#if NODE_103JT_AVAILABLE
#  include "sensors/jt103.h"
#endif
/* Misc */
#include "util/fixed_point.h"
#include "util/sensor_msg.h"
#if ENABLE_DBG
#  include "util/printf.h"
#else
#  define printf(...) do { } while (0)
#endif


/***** GLOBAL VARIABLES ***********************************************/
/* Variable (flag) for barrier synchronization */
uint8_t barrier = 1;
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
